KNwhile1/Water-Quality-Monitoring-System/Impressions3D/Boiter3DV1/PPS_Boitier.png

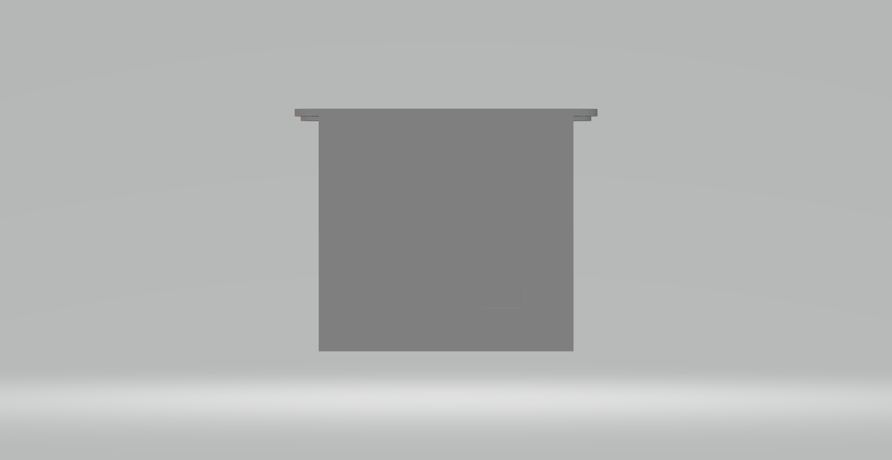
Impressions3D/Boiter3DV1/PPS_Boitier.png
