KNwhile1/Water-Quality-Monitoring-System/Impressions3D/Boiter3DV1/PPS_CouvercleBoitier.png

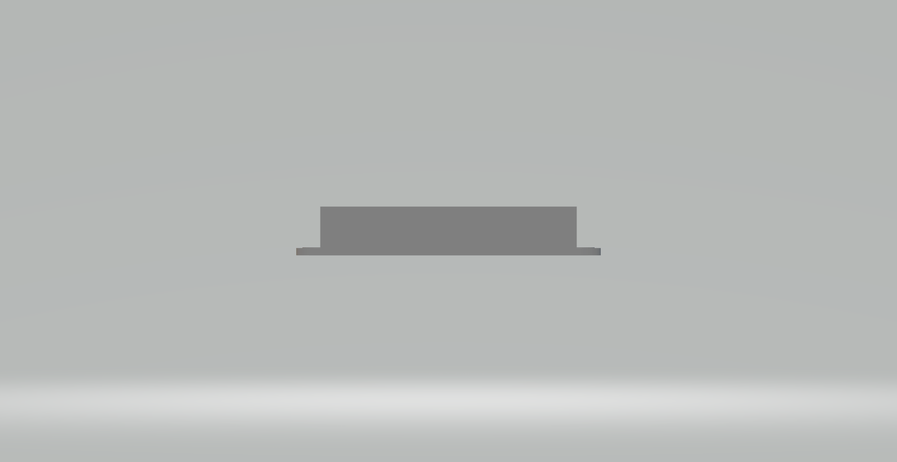
Impressions3D/Boiter3DV1/PPS_CouvercleBoitier.png
